TeamScheire/MiFlo/assets/sounds/headers/all.h

// This file was generated with the command-line:
//    /usr/local/bin/gd3asset -3 -f all.gd2 -o all.h f_bol.wav f_uitst.wav g_cool.wav g_formid.wav g_machti.wav g_stieva.wav g_woew.wav m_flink2.wav m_spinne.wav f_dduim.wav f_wauw.wav g_dduim2.wav g_goed.wav g_muppet.wav g_super.wav g_woop.wav m_flink3.wav m_super.wav f_go.wav g_allez.wav g_demax.wav g_goedzo.wav g_prima.wav g_tsjing.wav g_zogoed.wav m_gewel.wav f_komaan.wav g_bol.wav g_fantas.wav g_hopla.wav g_scool.wav g_wiii.wav m_flink.wav m_goed.wav

#define F_BOL 0UL
#define F_BOL_LENGTH 43776
#define F_BOL_FREQ 44100
#define F_UITST 43776UL
#define F_UITST_LENGTH 31680
#define F_UITST_FREQ 44100
#define G_COOL 75456UL
#define G_COOL_LENGTH 14976
#define G_COOL_FREQ 44100
#define G_FORMID 90432UL
#define G_FORMID_LENGTH 23040
#define G_FORMID_FREQ 44100
#define G_MACHTI 113472UL
#define G_MACHTI_LENGTH 27648
#define G_MACHTI_FREQ 44100
#define G_STIEVA 141120UL
#define G_STIEVA_LENGTH 16128
#define G_STIEVA_FREQ 44100
#define G_WOEW 157248UL
#define G_WOEW_LENGTH 33408
#define G_WOEW_FREQ 44100
#define M_FLINK2 190656UL
#define M_FLINK2_LENGTH 21888
#define M_FLINK2_FREQ 44100
#define M_SPINNE 212544UL
#define M_SPINNE_LENGTH 45504
#define M_SPINNE_FREQ 44100
#define F_DDUIM 258048UL
#define F_DDUIM_LENGTH 26496
#define F_DDUIM_FREQ 44100
#define F_WAUW 284544UL
#define F_WAUW_LENGTH 24768
#define F_WAUW_FREQ 44100
#define G_DDUIM2 309312UL
#define G_DDUIM2_LENGTH 19008
#define G_DDUIM2_FREQ 44100
#define G_GOED 328320UL
#define G_GOED_LENGTH 21888
#define G_GOED_FREQ 44100
#define G_MUPPET 350208UL
#define G_MUPPET_LENGTH 31680
#define G_MUPPET_FREQ 44100
#define G_SUPER 381888UL
#define G_SUPER_LENGTH 42624
#define G_SUPER_FREQ 44100
#define G_WOOP 424512UL
#define G_WOOP_LENGTH 17280
#define G_WOOP_FREQ 44100
#define M_FLINK3 441792UL
#define M_FLINK3_LENGTH 31104
#define M_FLINK3_FREQ 44100
#define M_SUPER 472896UL
#define M_SUPER_LENGTH 24192
#define M_SUPER_FREQ 44100
#define F_GO 497088UL
#define F_GO_LENGTH 19008
#define F_GO_FREQ 44100
#define G_ALLEZ 516096UL
#define G_ALLEZ_LENGTH 23616
#define G_ALLEZ_FREQ 44100
#define G_DEMAX 539712UL
#define G_DEMAX_LENGTH 18432
#define G_DEMAX_FREQ 44100
#define G_GOEDZO 558144UL
#define G_GOEDZO_LENGTH 20160
#define G_GOEDZO_FREQ 44100
#define G_PRIMA 578304UL
#define G_PRIMA_LENGTH 12096
#define G_PRIMA_FREQ 44100
#define G_TSJING 590400UL
#define G_TSJING_LENGTH 38592
#define G_TSJING_FREQ 44100
#define G_ZOGOED 628992UL
#define G_ZOGOED_LENGTH 17856
#define G_ZOGOED_FREQ 44100
#define M_GEWEL 646848UL
#define M_GEWEL_LENGTH 29952
#define M_GEWEL_FREQ 44100
#define F_KOMAAN 676800UL
#define F_KOMAAN_LENGTH 25920
#define F_KOMAAN_FREQ 44100
#define G_BOL 702720UL
#define G_BOL_LENGTH 38016
#define G_BOL_FREQ 44100
#define G_FANTAS 740736UL
#define G_FANTAS_LENGTH 25920
#define G_FANTAS_FREQ 44100
#define G_HOPLA 766656UL
#define G_HOPLA_LENGTH 12672
#define G_HOPLA_FREQ 44100
#define G_SCOOL 779328UL
#define G_SCOOL_LENGTH 27072
#define G_SCOOL_FREQ 44100
#define G_WIII 806400UL
#define G_WIII_LENGTH 30528
#define G_WIII_FREQ 44100
#define M_FLINK 836928UL
#define M_FLINK_LENGTH 23616
#define M_FLINK_FREQ 44100
#define M_GOED 860544UL
#define M_GOED_LENGTH 25920
#define M_GOED_FREQ 44100
#define ASSETS_END 886464UL
#define LOAD_ASSETS()  (GD.safeload("all.gd2"), GD.loadptr = ASSETS_END)

struct {
} bitmaps = {

};
