TeamScheire/MiFlo/assets/sounds/headers/generic.h

// This file was generated with the command-line:
//    /usr/local/bin/gd3asset -3 -f generic.gd2 -o generic.h g_allez.wav g_dduim2.wav g_formid.wav g_hopla.wav g_prima.wav g_super.wav g_woew.wav g_bol.wav g_demax.wav g_goed.wav g_machti.wav g_scool.wav g_tsjing.wav g_woop.wav g_cool.wav g_fantas.wav g_goedzo.wav g_muppet.wav g_stieva.wav g_wiii.wav g_zogoed.wav

#define G_ALLEZ 0UL
#define G_ALLEZ_LENGTH 23616
#define G_ALLEZ_FREQ 44100
#define G_DDUIM2 23616UL
#define G_DDUIM2_LENGTH 19008
#define G_DDUIM2_FREQ 44100
#define G_FORMID 42624UL
#define G_FORMID_LENGTH 23040
#define G_FORMID_FREQ 44100
#define G_HOPLA 65664UL
#define G_HOPLA_LENGTH 12672
#define G_HOPLA_FREQ 44100
#define G_PRIMA 78336UL
#define G_PRIMA_LENGTH 12096
#define G_PRIMA_FREQ 44100
#define G_SUPER 90432UL
#define G_SUPER_LENGTH 42624
#define G_SUPER_FREQ 44100
#define G_WOEW 133056UL
#define G_WOEW_LENGTH 33408
#define G_WOEW_FREQ 44100
#define G_BOL 166464UL
#define G_BOL_LENGTH 38016
#define G_BOL_FREQ 44100
#define G_DEMAX 204480UL
#define G_DEMAX_LENGTH 18432
#define G_DEMAX_FREQ 44100
#define G_GOED 222912UL
#define G_GOED_LENGTH 21888
#define G_GOED_FREQ 44100
#define G_MACHTI 244800UL
#define G_MACHTI_LENGTH 27648
#define G_MACHTI_FREQ 44100
#define G_SCOOL 272448UL
#define G_SCOOL_LENGTH 27072
#define G_SCOOL_FREQ 44100
#define G_TSJING 299520UL
#define G_TSJING_LENGTH 38592
#define G_TSJING_FREQ 44100
#define G_WOOP 338112UL
#define G_WOOP_LENGTH 17280
#define G_WOOP_FREQ 44100
#define G_COOL 355392UL
#define G_COOL_LENGTH 14976
#define G_COOL_FREQ 44100
#define G_FANTAS 370368UL
#define G_FANTAS_LENGTH 25920
#define G_FANTAS_FREQ 44100
#define G_GOEDZO 396288UL
#define G_GOEDZO_LENGTH 20160
#define G_GOEDZO_FREQ 44100
#define G_MUPPET 416448UL
#define G_MUPPET_LENGTH 31680
#define G_MUPPET_FREQ 44100
#define G_STIEVA 448128UL
#define G_STIEVA_LENGTH 16128
#define G_STIEVA_FREQ 44100
#define G_WIII 464256UL
#define G_WIII_LENGTH 30528
#define G_WIII_FREQ 44100
#define G_ZOGOED 494784UL
#define G_ZOGOED_LENGTH 17856
#define G_ZOGOED_FREQ 44100
#define ASSETS_END 512640UL
#define LOAD_ASSETS()  (GD.safeload("generic.gd2"), GD.loadptr = ASSETS_END)

struct {
} bitmaps = {

};
