TeamScheire/MiFlo/assets/sounds/headers/genminne.h

// This file was generated with the command-line:
//    /usr/local/bin/gd3asset -3 -f genminne.gd2 -o genminne.h g_cool.wav g_formid.wav g_machti.wav g_stieva.wav g_woew.wav g_dduim2.wav g_goed.wav g_muppet.wav g_super.wav g_woop.wav g_allez.wav g_demax.wav g_goedzo.wav g_prima.wav g_tsjing.wav g_zogoed.wav g_bol.wav g_fantas.wav g_hopla.wav g_scool.wav g_wiii.wav m_flink3.wav m_super.wav m_gewel.wav m_flink.wav m_goed.wav m_flink2.wav m_spinne.wav

#define G_COOL 0UL
#define G_COOL_LENGTH 14976
#define G_COOL_FREQ 44100
#define G_FORMID 14976UL
#define G_FORMID_LENGTH 23040
#define G_FORMID_FREQ 44100
#define G_MACHTI 38016UL
#define G_MACHTI_LENGTH 27648
#define G_MACHTI_FREQ 44100
#define G_STIEVA 65664UL
#define G_STIEVA_LENGTH 16128
#define G_STIEVA_FREQ 44100
#define G_WOEW 81792UL
#define G_WOEW_LENGTH 33408
#define G_WOEW_FREQ 44100
#define G_DDUIM2 115200UL
#define G_DDUIM2_LENGTH 19008
#define G_DDUIM2_FREQ 44100
#define G_GOED 134208UL
#define G_GOED_LENGTH 21888
#define G_GOED_FREQ 44100
#define G_MUPPET 156096UL
#define G_MUPPET_LENGTH 31680
#define G_MUPPET_FREQ 44100
#define G_SUPER 187776UL
#define G_SUPER_LENGTH 42624
#define G_SUPER_FREQ 44100
#define G_WOOP 230400UL
#define G_WOOP_LENGTH 17280
#define G_WOOP_FREQ 44100
#define G_ALLEZ 247680UL
#define G_ALLEZ_LENGTH 23616
#define G_ALLEZ_FREQ 44100
#define G_DEMAX 271296UL
#define G_DEMAX_LENGTH 18432
#define G_DEMAX_FREQ 44100
#define G_GOEDZO 289728UL
#define G_GOEDZO_LENGTH 20160
#define G_GOEDZO_FREQ 44100
#define G_PRIMA 309888UL
#define G_PRIMA_LENGTH 12096
#define G_PRIMA_FREQ 44100
#define G_TSJING 321984UL
#define G_TSJING_LENGTH 38592
#define G_TSJING_FREQ 44100
#define G_ZOGOED 360576UL
#define G_ZOGOED_LENGTH 17856
#define G_ZOGOED_FREQ 44100
#define G_BOL 378432UL
#define G_BOL_LENGTH 38016
#define G_BOL_FREQ 44100
#define G_FANTAS 416448UL
#define G_FANTAS_LENGTH 25920
#define G_FANTAS_FREQ 44100
#define G_HOPLA 442368UL
#define G_HOPLA_LENGTH 12672
#define G_HOPLA_FREQ 44100
#define G_SCOOL 455040UL
#define G_SCOOL_LENGTH 27072
#define G_SCOOL_FREQ 44100
#define G_WIII 482112UL
#define G_WIII_LENGTH 30528
#define G_WIII_FREQ 44100
#define M_FLINK3 512640UL
#define M_FLINK3_LENGTH 31104
#define M_FLINK3_FREQ 44100
#define M_SUPER 543744UL
#define M_SUPER_LENGTH 24192
#define M_SUPER_FREQ 44100
#define M_GEWEL 567936UL
#define M_GEWEL_LENGTH 29952
#define M_GEWEL_FREQ 44100
#define M_FLINK 597888UL
#define M_FLINK_LENGTH 23616
#define M_FLINK_FREQ 44100
#define M_GOED 621504UL
#define M_GOED_LENGTH 25920
#define M_GOED_FREQ 44100
#define M_FLINK2 647424UL
#define M_FLINK2_LENGTH 21888
#define M_FLINK2_FREQ 44100
#define M_SPINNE 669312UL
#define M_SPINNE_LENGTH 45504
#define M_SPINNE_FREQ 44100
#define ASSETS_END 714816UL
#define LOAD_ASSETS()  (GD.safeload("genminne.gd2"), GD.loadptr = ASSETS_END)

struct {
} bitmaps = {

};
