TeamScheire/MiFlo/assets/sounds/headers/minne.h

// This file was generated with the command-line:
//    /usr/local/bin/gd3asset -3 -f minne.gd2 -o minne.h m_flink3.wav m_super.wav m_gewel.wav m_flink.wav m_goed.wav m_flink2.wav m_spinne.wav

#define M_FLINK3 0UL
#define M_FLINK3_LENGTH 31104
#define M_FLINK3_FREQ 44100
#define M_SUPER 31104UL
#define M_SUPER_LENGTH 24192
#define M_SUPER_FREQ 44100
#define M_GEWEL 55296UL
#define M_GEWEL_LENGTH 29952
#define M_GEWEL_FREQ 44100
#define M_FLINK 85248UL
#define M_FLINK_LENGTH 23616
#define M_FLINK_FREQ 44100
#define M_GOED 108864UL
#define M_GOED_LENGTH 25920
#define M_GOED_FREQ 44100
#define M_FLINK2 134784UL
#define M_FLINK2_LENGTH 21888
#define M_FLINK2_FREQ 44100
#define M_SPINNE 156672UL
#define M_SPINNE_LENGTH 45504
#define M_SPINNE_FREQ 44100
#define ASSETS_END 202176UL
#define LOAD_ASSETS()  (GD.safeload("minne.gd2"), GD.loadptr = ASSETS_END)

struct {
} bitmaps = {

};
