TeamScheire/MiFlo/arduino/miflo/settings_example.h

const char* person = "name";

const char* ssid = "SSID";
const char* password =  "PASSWORD";

const char* mqttServer = "BROKER";
const int mqttPort = 1883;
const char* mqttTopic = "TOPIC"; // e.g. /iot/miflo/minne/timer"
const char* mqttClient = "CLIENTNAME";
